Tecsmith/flying-horse-foot/Firmware/QMK/keyboards/bpiphany/pegasushoof/2021/2021.c

/*
Copyright 2016 Daniel Svensson <dsvensson@gmail.com>
Copyright 2021 Silvino Rodrigues <github.com/silvinor>

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
You should have received a copy of the GNU General Public License
along with this program.  If not, see <http://www.gnu.org/licenses/>.
*/

#include "2021.h"


extern inline void ph_caps_led_on(void);
extern inline void ph_caps_led_off(void);

extern inline void ph_sclk_led_on(void);
extern inline void ph_sclk_led_off(void);
